miguel-fg/braille-printer/stl files/backbonemk2.STL

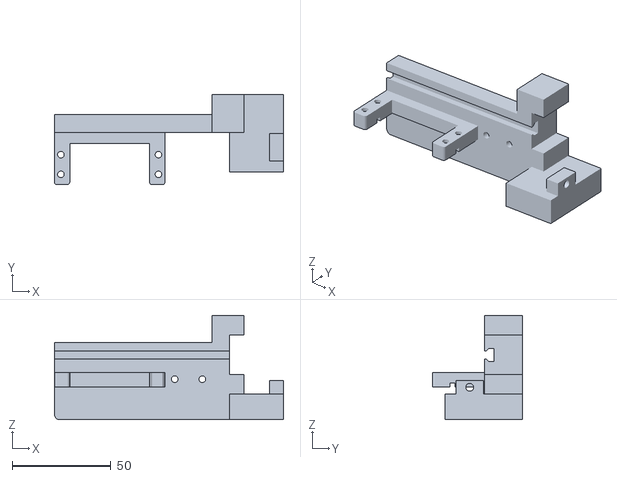
[picture p15: CAD file, 2023-06-08]
stl files/backbonemk2.STL
116.2 x 45.9 x 52.9
