miguel-fg/braille-printer/stl files/Motor_Bracket_Mini_Version.STL

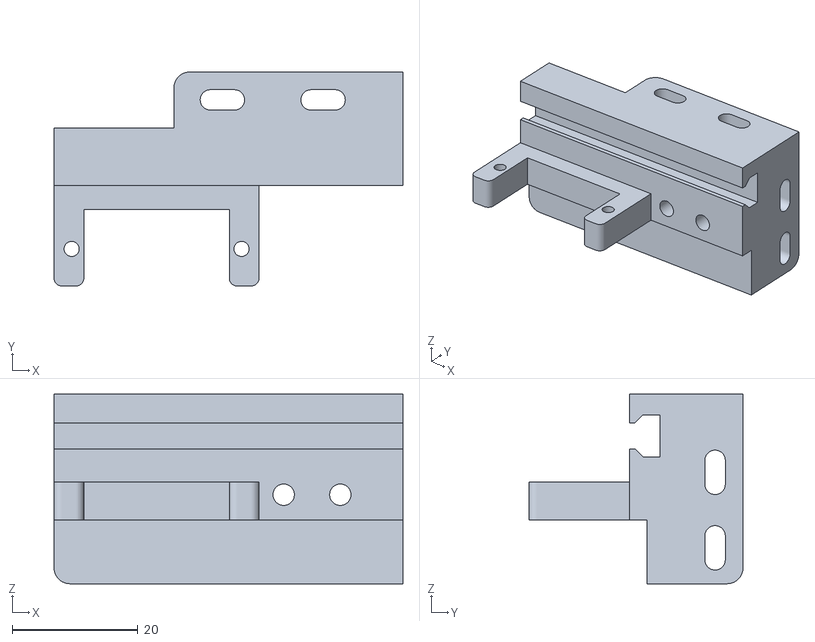
[picture p16: CAD file, 2023-06-08]
stl files/Motor_Bracket_Mini_Version.STL
55.5 x 34.0 x 30.1
