miguel-fg/braille-printer/stl files/roller.STL

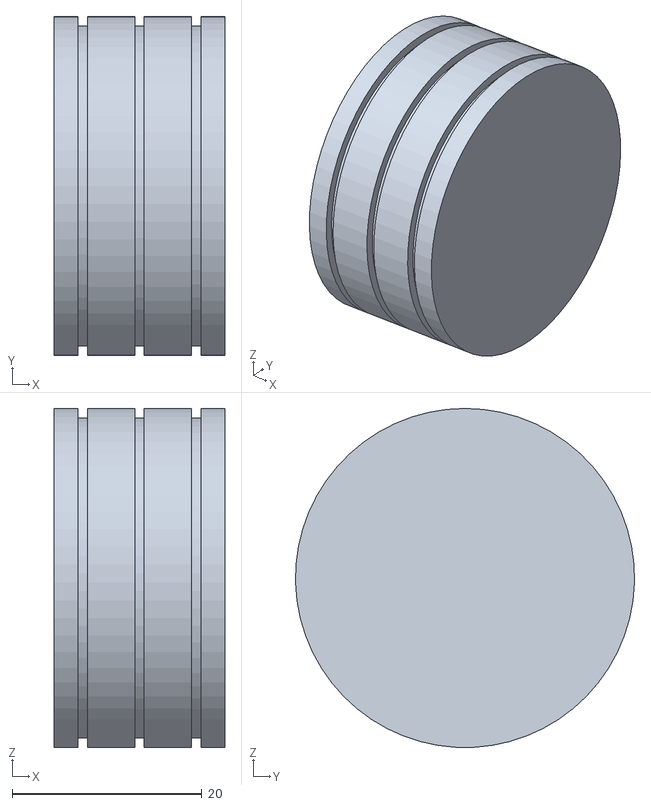
[picture p17: CAD file, 2023-06-08]
stl files/roller.STL
18.0 x 35.7 x 35.7
