miguel-fg/braille-printer/stl files/Motor_Bracket_Large_Version.STL

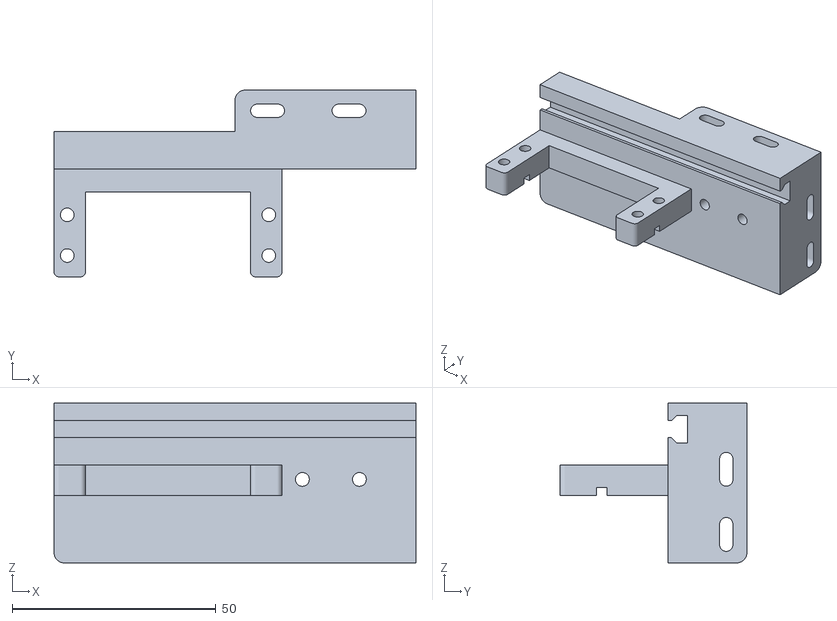
[picture p18: CAD file, 2023-06-08]
stl files/Motor_Bracket_Large_Version.STL
88.9 x 45.9 x 39.2
