miguel-fg/braille-printer/stl files/Fan_blade_openscad.stl

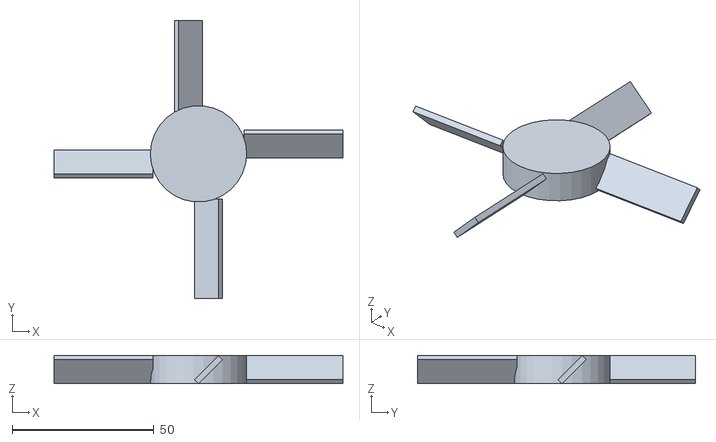
[picture p19: CAD file, 2023-06-08]
stl files/Fan_blade_openscad.stl
102.0 x 98.0 x 10.0
