miguel-fg/braille-printer/stl files/rod.STL

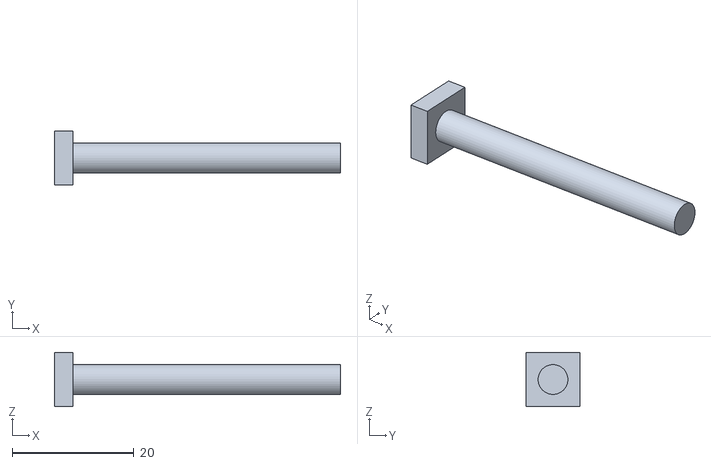
[picture p20: CAD file, 2023-06-08]
stl files/rod.STL
47.0 x 8.88 x 8.88
