miguel-fg/braille-printer/stl files/rodillofinal.STL

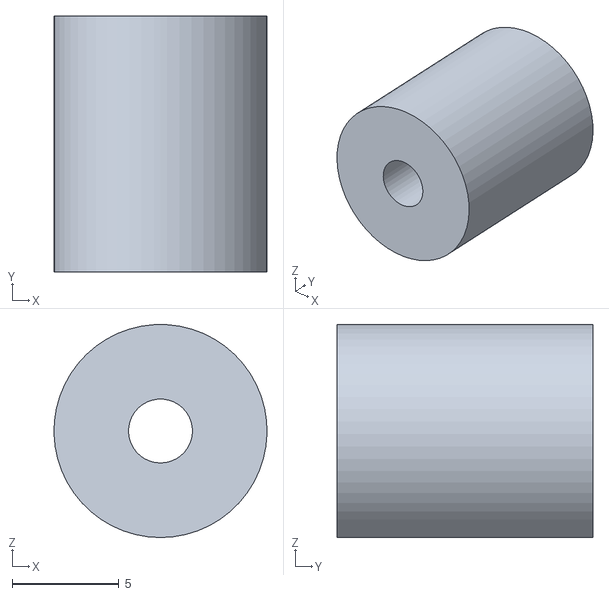
[picture p21: CAD file, 2023-06-08]
stl files/rodillofinal.STL
10.00 x 12.0 x 10.0
