miguel-fg/braille-printer/stl files/Pusher_150mm_Long.STL

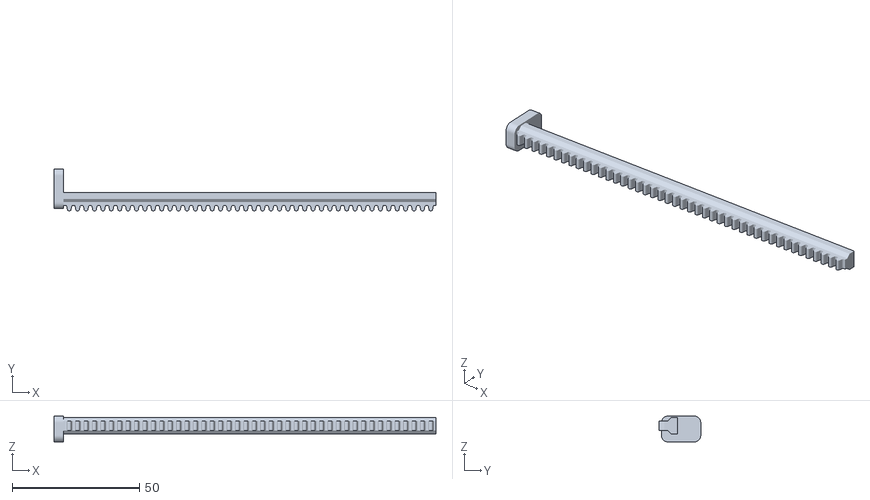
[picture p22: CAD file, 2023-06-08]
stl files/Pusher_150mm_Long.STL
150.0 x 16.3 x 10.2
