miguel-fg/braille-printer/stl files/MotCCap.stl

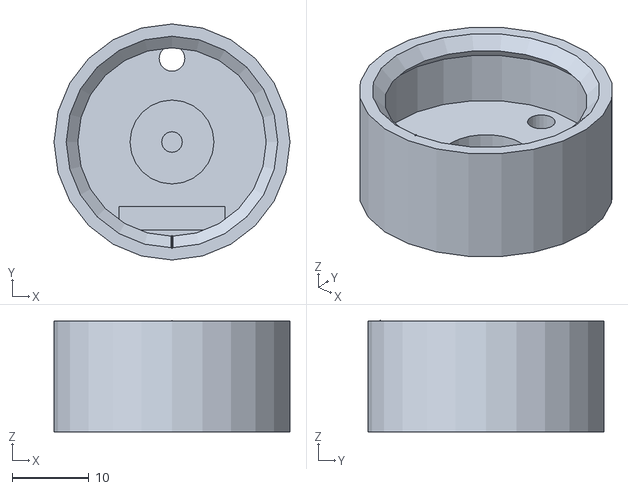
[picture p23: CAD file, 2023-06-08]
stl files/MotCCap.stl
30.8 x 30.8 x 14.5
