miguel-fg/braille-printer/stl files/Raspberry_Pi_4b_Case_-_Cap.stl

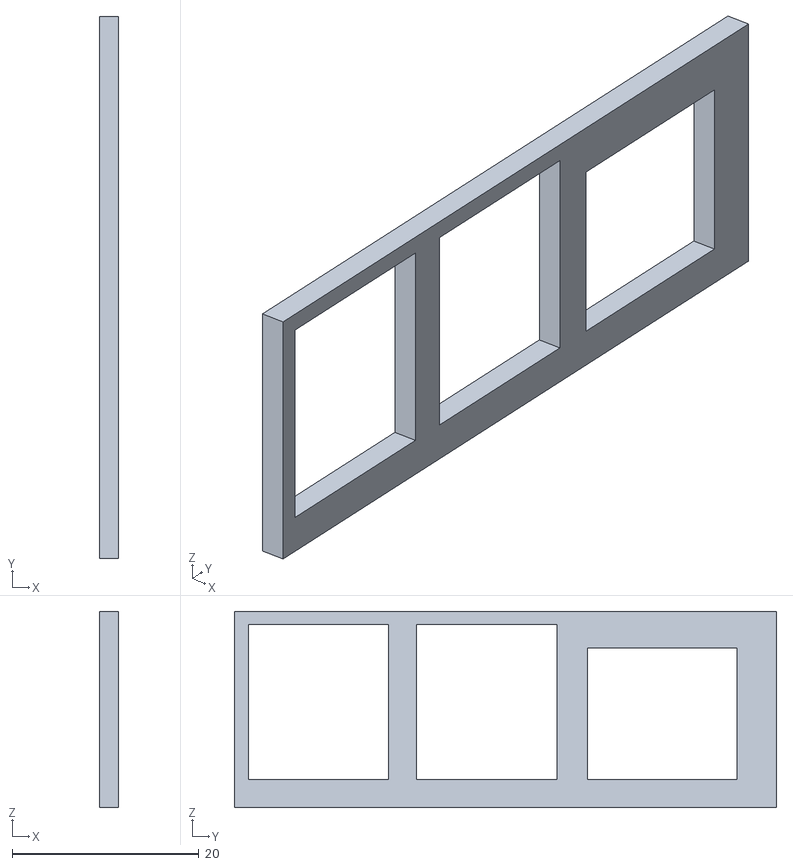
[picture p24: CAD file, 2023-06-08]
stl files/Raspberry_Pi_4b_Case_-_Cap.stl
2.00 x 58.0 x 21.0
